zjuwangrui/21A-Distortion-Mearsurement/resources/figure/50k测量/信号发生器.jpg

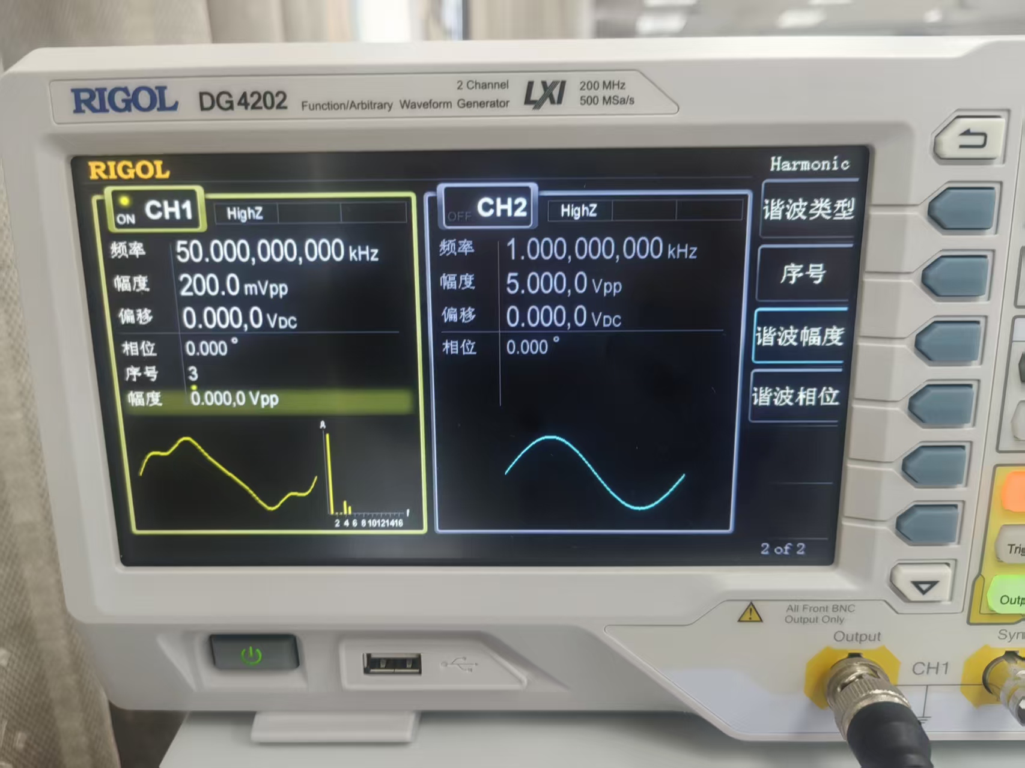
resources/figure/50k测量/信号发生器.jpg
