zjuwangrui/21A-Distortion-Mearsurement/resources/实物连接图.jpg

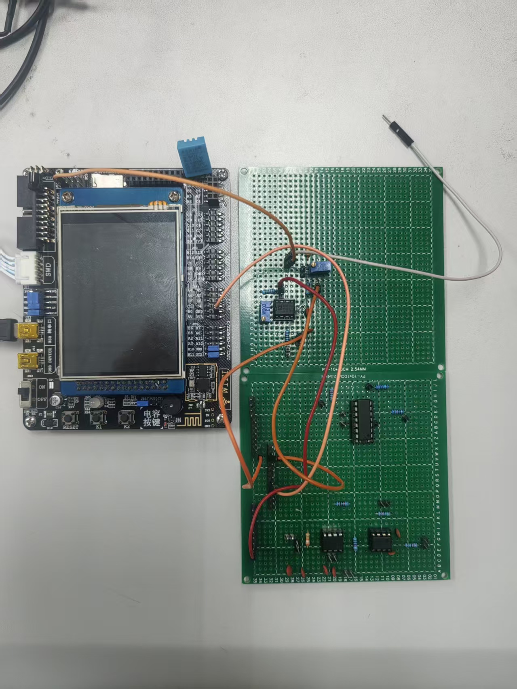
resources/实物连接图.jpg
