zjuwangrui/21A-Distortion-Mearsurement/resources/测评表2.jpg

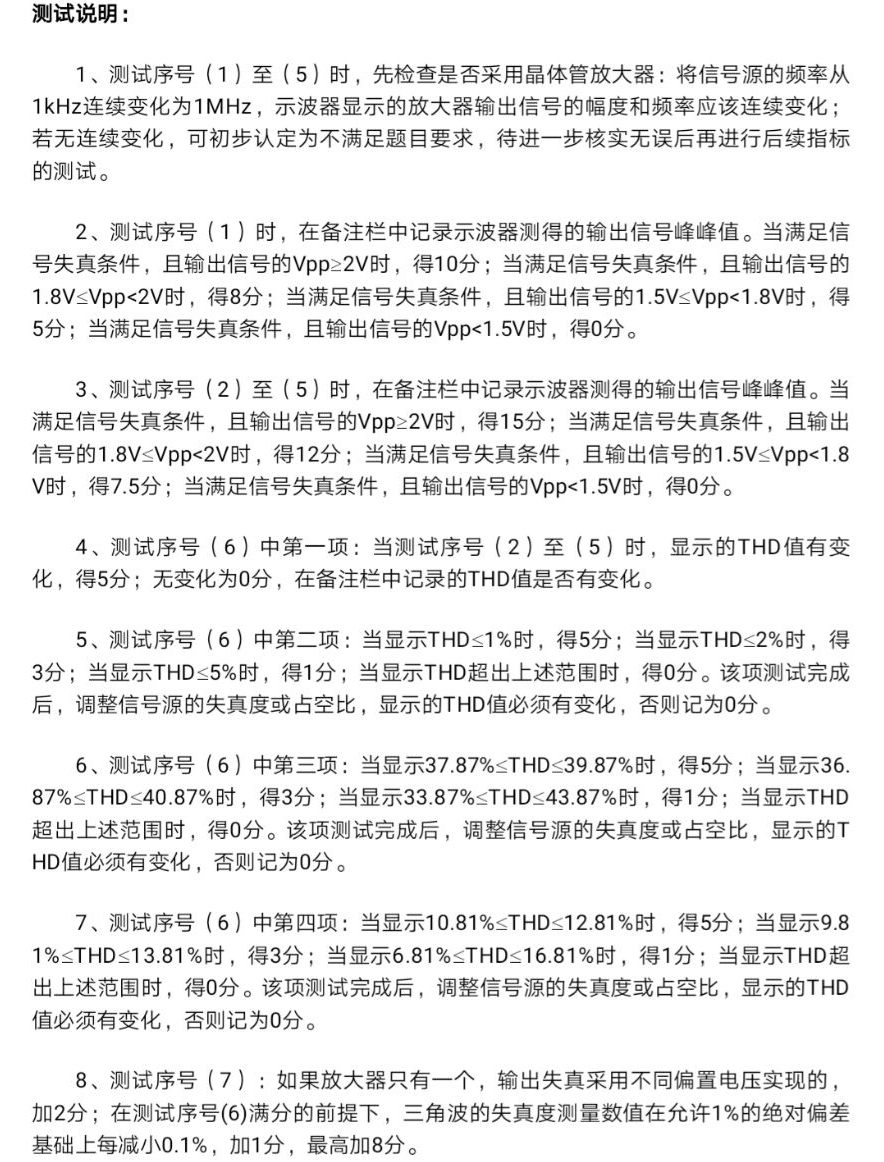
resources/测评表2.jpg
