zjuwangrui/21A-Distortion-Mearsurement/resources/测评表.jpg

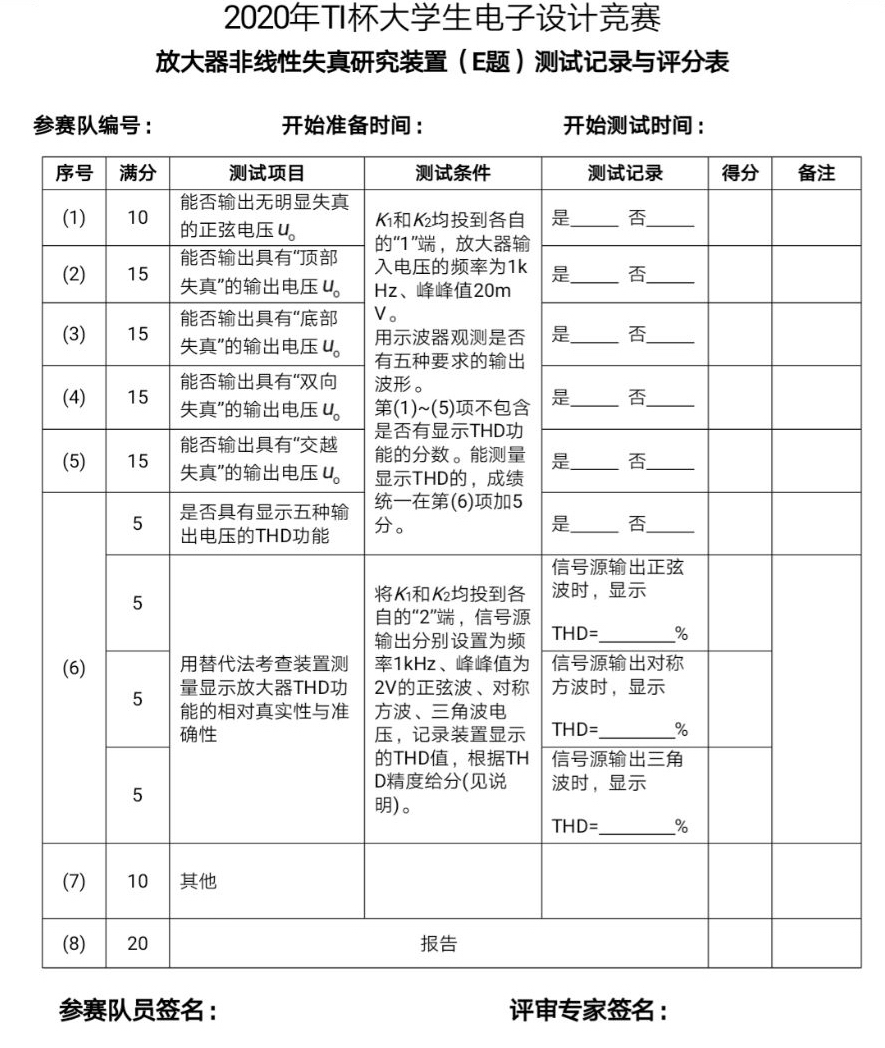
resources/测评表.jpg
