zjuwangrui/21A-Distortion-Mearsurement/resources/省二等奖-ZJA434-信电13组-A题-报告及资料（更新）/code/Wave_Display_Screen/images/1.png

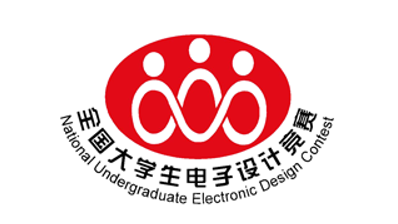
resources/省二等奖-ZJA434-信电13组-A题-报告及资料（更新）/code/Wave_Display_Screen/images/1.png
