zjuwangrui/21A-Distortion-Mearsurement/hardware/stimulation/filter.asc

C1: cap; 220n
C2: cap; 100n
C3: cap; 220n
C4: cap; 220n
C5: cap; 1n
C6: cap; 1µ
R1: res; 5.6k
R2: res; 5.6k
R3: res; 10k
R4: res; 10k
R5: res; 10k
R6: res; 100
R7: res; 5k
R8: res; 4k
R9: res; 10k
U1: LTC6362
V1: voltage; SINE(0 300 1k); AC 100m
V2: voltage; 5V
Named nets: Vin, 0, dc, ac, Vcc, Vo, Vref
.ac dec 1000 100 10Meg
.tran 0 5m 1n 5u
