zjuwangrui/21A-Distortion-Mearsurement/src/bsp/spi.c

#include "bsp/spi.h"

SPI_HandleTypeDef hspi1;

/* SPI1 GPIO：
 *   PA5  SCK    AF_PP  高速
 *   PA6  MISO   浮空输入
 *   PA7  MOSI   AF_PP  高速
 * CS 各外设自己在自己驱动里配置，不占用 SPI 模块。
 */
void MX_SPI1_Init(void)
{
    __HAL_RCC_SPI1_CLK_ENABLE();
    __HAL_RCC_GPIOA_CLK_ENABLE();

    GPIO_InitTypeDef g = {0};

    g.Pin   = GPIO_PIN_5 | GPIO_PIN_7;   /* SCK, MOSI */
    g.Mode  = GPIO_MODE_AF_PP;
    g.Speed = GPIO_SPEED_FREQ_HIGH;
    HAL_GPIO_Init(GPIOA, &g);

    g.Pin   = GPIO_PIN_6;                /* MISO */
    g.Mode  = GPIO_MODE_INPUT;
    g.Pull  = GPIO_NOPULL;
    HAL_GPIO_Init(GPIOA, &g);

    hspi1.Instance               = SPI1;
    hspi1.Init.Mode              = SPI_MODE_MASTER;
    hspi1.Init.Direction         = SPI_DIRECTION_2LINES;
    hspi1.Init.DataSize          = SPI_DATASIZE_8BIT;
    hspi1.Init.CLKPolarity       = SPI_POLARITY_LOW;      /* Mode 0 */
    hspi1.Init.CLKPhase          = SPI_PHASE_1EDGE;
    hspi1.Init.NSS               = SPI_NSS_SOFT;          /* CS 软件控制 */
    hspi1.Init.BaudRatePrescaler = SPI_BAUDRATEPRESCALER_8;  /* 72M/8 = 9MHz */
    hspi1.Init.FirstBit          = SPI_FIRSTBIT_MSB;
    hspi1.Init.TIMode            = SPI_TIMODE_DISABLE;
    hspi1.Init.CRCCalculation    = SPI_CRCCALCULATION_DISABLE;
    hspi1.Init.CRCPolynomial     = 7;
    if (HAL_SPI_Init(&hspi1) != HAL_OK) while (1);
}

uint8_t SPI1_Xfer(uint8_t tx)
{
    uint8_t rx = 0;
    HAL_SPI_TransmitReceive(&hspi1, &tx, &rx, 1, HAL_MAX_DELAY);
    return rx;
}

void SPI1_Write(const uint8_t *data, uint16_t len)
{
    HAL_SPI_Transmit(&hspi1, (uint8_t *)data, len, HAL_MAX_DELAY);
}

void SPI1_Xchg(const uint8_t *tx, uint8_t *rx, uint16_t len)
{
    HAL_SPI_TransmitReceive(&hspi1, (uint8_t *)tx, rx, len, HAL_MAX_DELAY);
}
