zjuwangrui/21A-Distortion-Mearsurement/export_hex.py

Import("env")
 
# # Custom HEX from ELF
 
env.AddPostAction(
 
    "$BUILD_DIR/${PROGNAME}.elf",
 
    env.VerboseAction(" ".join([
 
        "$OBJCOPY", "-O", "ihex", "-R", ".eeprom",
 
        '"$BUILD_DIR/${PROGNAME}.elf"', '"$BUILD_DIR/${PROGNAME}.hex"'  # 加个单引号
 
    ]), "Building $BUILD_DIR/${PROGNAME}.hex")
 
)
